wrobel111/Audi-CDC-Emulator/Software/cdc_arduino_atmega328pb_bk3254/cdc_arduino_atmega328pb_bk3254.ino

/*****************************************************************************


   Audi/Volkswagen Audi Interface
   
   Target: arduino atmega328(tested)


   Orginal Author: Vincent

   Date: January, 2011

   Version: 0.01


   Originally ported from VWCDPIC Project:

   http://www.k9spud.com/vwcdpic/

   Ported from Matthias Koelling's AVR Code:

   www.mikrocontroller.net/attachment/31279/vwcdc.c

   ---------------------------------
   16. Mar 2015:

   https://github.com/tomaskovacik/
   arduino duemilanove works:

   RADIO PIN -> arduino pin

   DataOut   -> digital 8 (ICP1)
   DataIn    -> digital 11(PB3)
   Clock     -> digital 13(PB5)

   computer -> arduino pin
   serial TX -> digital 0 (PD0)
   serial RX -> digital 1 (PD1)

   19. Mar 2015  tomaskovacik
   port to atmega8

   14.Jun 2019 kovo
   this compile fine against mega324(P/A/PA/PB)
   
   ---------------------------------
   Mateusz Wrobel 24.05.2025
   - bluetooth BK3266 module 
   - telephone comunication (music and calling)
   - use Timer3 Atmega328PB instead Timer0



 *****************************************************************************/
#include "bk3254.h"
#include "cdc_function.h"
#include "Remote.h"
#include "led.h"
#include <SoftwareSerial.h>

extern BK3254 bt;
extern Remote remote;
extern SoftwareSerial BtSerial;

void setup()
{
  Serial.begin(9600);

  Serial.println("Start init");
  initLed();
  turnOnLed();
  bt.init();
  Init_VWCDC();
  remote.initRemote();
  Serial.println("Init finish");
  turnOffLed();

}
void loop()
{
  bt.checkState();
  CDC_Protocol(); 
  remote.protocol();
  updateLedStatus();
}
